davisonaudio/HapticInstrumentWorkshop/firmware/TeensyPlatformIO/include/ForceSensing.h

/*
 
ForceSensing.h
 
Author: Matt Davison
Date: 14/06/2024
 
*/

#pragma once

#include "au_GoertzelAlgorithm.h"
#include "au_Windowing.h"
#include "au_Onepole.h"

class ForceSensing
{
public:

    void setup();
    //Returns actual freq value (due to integer rounding)
    sample_t setResonantFrequencyHz(sample_t resonant_freq_hz);
    void setWindowSizePeriods(int window_size_periods);

    bool valueAvailable();

    void process(sample_t actuation_sample, sample_t sensed_sample);

    sample_t getDamping();
    int getWindowSizeSamples();
    int getWindowSizePeriods();

    /* 
     * This function should be called when the transducer is damped. it stores the last raw val as the calibration value
     * Note: make sure at least 1 window length has passed with the actuator damped before calling this function
     * Also ensure that there is a tone at the resonant frequency, at the required signal level, before calibrating.
     */
    void calibrateDamped();

    /* 
     * This function should be called when the transducer is undamped. it stores the last raw val as the calibration value
     * Note: make sure at least 1 window length has passed with the actuator undamped before calling this function
     * Also ensure that there is a tone at the resonant frequency, at the required signal level, before calibrating.
     */
    void calibrateUndamped();

    void setRawDampedValue(float raw_damped);
    void setRawUndampedValue(float raw_undamped);

    sample_t getRawDampedValue();
    sample_t getRawUndampedValue();

    void setRawDebugPrint(bool enable_print);

    virtual void endOfWindow(){}

    /*
     * Resets indexes of Goertzel & Windowing object, restarts them at beginning of the window.
     * It also resets the windowing object window sizes to be equal to the goertzel object window lengths (in case of freq/period length change)
     */
    void reset();

private:

    RealtimeGoertzel m_actuation_signal_goertzel;
    RealtimeGoertzel m_sensed_signal_goertzel;

    Windowing m_actuation_signal_window;
    Windowing m_sensing_signal_window;

    Onepole m_force_sense_averaging;

    /*
     * Returns a normalised floating point value of the damping where 1 = undamped, 0 = damped
     * Note: damped & undamped calibration methods must be called first, otherwise this function won't do anything useful
     */
    sample_t mapRawValue(sample_t raw_val);

    sample_t m_undamped_calibration_val;
    sample_t m_damped_calibration_val;

    sample_t m_last_raw_difference_val;
    sample_t m_last_mapped_filtered_val;

    bool m_debug_raw_print_enabled = false;
    bool m_new_val_flag = false;

};


/*
 * ForceSensing Implementation
 */
void ForceSensing::setup()
{
    GoertzelAlgorithm::SetupParameters setup_parameters;
    setup_parameters.sample_rate = AUDIO_SAMPLE_RATE_EXACT;
    setup_parameters.target_frequency = 440.0;
    setup_parameters.window_size_periods = 1;

    m_actuation_signal_goertzel.setup(setup_parameters);
    m_sensed_signal_goertzel.setup(setup_parameters);

    m_force_sense_averaging.setB1(-0.7);

    reset();
}

sample_t ForceSensing::setResonantFrequencyHz(sample_t resonant_freq_hz)
{
    sample_t actual_freq = m_actuation_signal_goertzel.setTargetFrequencyHz(resonant_freq_hz);
    m_sensed_signal_goertzel.setTargetFrequencyHz(resonant_freq_hz);

    reset();
    return actual_freq;
}

void ForceSensing::setWindowSizePeriods(int window_size_periods)
{
    m_actuation_signal_goertzel.setWindowSizePeriods(window_size_periods);
    m_sensed_signal_goertzel.setWindowSizePeriods(window_size_periods);

    reset();
}

bool ForceSensing::valueAvailable()
{
    bool flag_state = m_new_val_flag;
    m_new_val_flag = false; //reset flag
    return flag_state;
}

void ForceSensing::process(sample_t actuation_sample, sample_t sensed_sample)
{
    //Apply window to signals & feed into Goertzel
    m_actuation_signal_goertzel.processSample(m_actuation_signal_window.applyWindowToSample(actuation_sample));
    m_sensed_signal_goertzel.processSample(m_sensing_signal_window.applyWindowToSample(sensed_sample));
    if (m_actuation_signal_goertzel.checkNewValFlag())
    {
        m_last_raw_difference_val = m_actuation_signal_goertzel.getLastMagnitude() - m_sensed_signal_goertzel.getLastMagnitude();
        m_new_val_flag = true;
        m_last_mapped_filtered_val = m_force_sense_averaging.process(mapRawValue(m_last_raw_difference_val));
        if (m_debug_raw_print_enabled)
        {
            printf("Raw force sense vals: actuation: %f, sense: %f \r\n",m_actuation_signal_goertzel.getLastMagnitude(), m_sensed_signal_goertzel.getLastMagnitude());
        }

        // printf("Actuate: %f, Sense: %f, Diff: %f\r\n", m_actuation_signal_goertzel.getLastPhase(), m_sensed_signal_goertzel.getLastPhase(), m_actuation_signal_goertzel.getLastPhase() -  m_sensed_signal_goertzel.getLastPhase());
        //  printf("Actuate:\r\n");
    }
}

sample_t ForceSensing::getDamping()
{
    return m_last_mapped_filtered_val;
}

int ForceSensing::getWindowSizeSamples()
{
    return m_actuation_signal_goertzel.getWindowLengthSamples();
}

int ForceSensing::getWindowSizePeriods()
{
    return m_actuation_signal_goertzel.getWindowLengthPeriods();
}

void ForceSensing::calibrateUndamped()
{
    m_undamped_calibration_val = m_last_raw_difference_val;
    printf("New undamped calibration value: %f \r\n", m_undamped_calibration_val);
}

void ForceSensing::calibrateDamped()
{
    m_damped_calibration_val = m_last_raw_difference_val;
    printf("New damped calibration value: %f \r\n", m_damped_calibration_val);
}

sample_t ForceSensing::mapRawValue(sample_t raw_val)
{
    sample_t value_range = m_undamped_calibration_val - m_damped_calibration_val;
    sample_t mapped_val = (raw_val - m_damped_calibration_val) / value_range;
    if (mapped_val < 0.0)
    {
        mapped_val = 0.0;
    }
    if (mapped_val > 1.0)
    {
        mapped_val = 1.0;
    }
    return mapped_val;
}

void ForceSensing::reset()
{
    m_actuation_signal_goertzel.reset();
    m_sensed_signal_goertzel.reset();
    
    m_actuation_signal_window.resetIndex();
    m_sensing_signal_window.resetIndex();

    m_actuation_signal_window.setWindowSizeSamples(m_actuation_signal_goertzel.getWindowLengthSamples());
    m_sensing_signal_window.setWindowSizeSamples(m_sensed_signal_goertzel.getWindowLengthSamples());
}

void ForceSensing::setRawDampedValue(float raw_damped)
{
    m_damped_calibration_val = raw_damped;
}

void ForceSensing::setRawUndampedValue(float raw_undamped)
{
    m_undamped_calibration_val = raw_undamped;
}

sample_t ForceSensing::getRawDampedValue()
{
    return m_damped_calibration_val;
}

sample_t ForceSensing::getRawUndampedValue()
{
    return m_undamped_calibration_val;
}

void ForceSensing::setRawDebugPrint(bool enable_print)
{
    m_debug_raw_print_enabled = enable_print;
}
