davisonaudio/HapticInstrumentWorkshop/firmware/TeensyPlatformIO/include/TeensyEeprom.h

/*

TeensyEeprom.h

Author: Matt Davison
Date: 13/11/2024

For more info on the Teensy EEPROM see: https://www.pjrc.com/teensy/td_libs_EEPROM.html

*/

#pragma once

//Include the Arduino EEPROM library
#include "EEPROM.h"
#include "AudioRouting.h"
#include "au_Biquad.h"


class TeensyEeprom
{
    /*
     * REGISTER MAP:
     * Floats stored first, then bytes
     */
    
    public:

        enum class FloatParameters
        {
            RESONANT_FREQUENCY_HZ = 0,
            RESONANT_GAIN_DB,
            RESONANT_Q,
            TONE_LEVEL_DB,
            INDUCTANCE_FILTER_COEFFICIENT,
            BROADBAND_GAIN_DB,
            SAMPLE_RATE_HZ,
            UNDAMPED_CALIBRATION_VALUE,
            DAMPED_CALIBRATION_VALUE,
            OUTPUT_LPF_CUTOFF_HZ,
            INPUT_LPF_CUTOFF_HZ,
            HEADPHONE_LEVEL_DB,
            ACTUATION_LEVEL_DB,
            INDUCTANCE_BQ_A0,
            INDUCTANCE_BQ_A1,
            INDUCTANCE_BQ_A2,
            INDUCTANCE_BQ_B1,
            INDUCTANCE_BQ_B2,

            NUM_FLOAT_PARAMETERS
        };

        enum class ByteParameters
        {
            SERIAL_NUMBER = 0,
            BOARD_REVISION,
            LAST_SAVED_MAJ_VERSION,
            LAST_SAVED_MIN_VERSION,
            GOERTZEL_WINDOW_LENGTH,
            AUDIO_SHIELD_MODE,
            
            NUM_BYTE_PARAMETERS = 128 // Leave buffer to enable additional byte parameters while maintaining backwards compatibility
        };



        static const int NUM_EEPROM_BYTES = 1080; //Correct for Teensy 4.0
        static constexpr int BYTES_PER_FLOAT = sizeof(float);

        
        static constexpr int BYTES_BASE = 0;
        static constexpr int FLOATS_BASE = BYTES_BASE + static_cast<int>(ByteParameters::NUM_BYTE_PARAMETERS);

        void write(ByteParameters byte_parameter, uint8_t value)
        {
            EEPROM.write(getEepromAddress(byte_parameter), value);
        }
        uint8_t read(ByteParameters byte_parameter)
        {
            return EEPROM.read(getEepromAddress(byte_parameter));
        }

        void write(FloatParameters float_parameter, float value)
        {
            writeFloat(getEepromAddress(float_parameter), value);
        }

        float read(FloatParameters float_parameter)
        {
            return readFloat(getEepromAddress(float_parameter));
        }

        void writeBoardRevision(AudioRouting::BoardRevision board_revision)
        {
            write(ByteParameters::BOARD_REVISION, static_cast<uint8_t>(board_revision));
        }

        AudioRouting::BoardRevision readBoardRevision()
        {
            return static_cast<AudioRouting::BoardRevision>(read(ByteParameters::BOARD_REVISION));
        }

        void writeAudioShieldMode(AudioRouting::AudioShieldMode shield_mode)
        {
            write(ByteParameters::AUDIO_SHIELD_MODE, static_cast<uint8_t>(shield_mode));
        }

        AudioRouting::AudioShieldMode readAudioShieldMode()
        {
            return static_cast<AudioRouting::AudioShieldMode>(read(ByteParameters::AUDIO_SHIELD_MODE));
        }

        void writeInductanceBiquad(Biquad::Coefficients coefficients)
        {
            write(FloatParameters::INDUCTANCE_BQ_A0, coefficients.a0);
            write(FloatParameters::INDUCTANCE_BQ_A1, coefficients.a1);
            write(FloatParameters::INDUCTANCE_BQ_A2, coefficients.a2);
            write(FloatParameters::INDUCTANCE_BQ_B1, coefficients.b1);
            write(FloatParameters::INDUCTANCE_BQ_B2, coefficients.b2);
        }

        Biquad::Coefficients readInductanceBiquad()
        {
            Biquad::Coefficients coefficients;
            coefficients.a0 = read(FloatParameters::INDUCTANCE_BQ_A0);
            coefficients.a1 = read(FloatParameters::INDUCTANCE_BQ_A1);
            coefficients.a2 = read(FloatParameters::INDUCTANCE_BQ_A2);
            coefficients.b1 = read(FloatParameters::INDUCTANCE_BQ_B1);
            coefficients.b2 = read(FloatParameters::INDUCTANCE_BQ_B2);
            return coefficients;
        }


    private:

        //Union is used to convert between float and bytes (sorry)
        union FloatByteConverter
        {
            float float_val;
            uint8_t byte_vals[sizeof(float)];
        };

        /*
         *
         *
         */
        void writeFloat(unsigned int eeprom_address, float float_to_write)
        {
            FloatByteConverter float_to_byte;
            float_to_byte.float_val = float_to_write;

            for (unsigned int i = 0 ; i < sizeof(float) ; i++ )
            {
                EEPROM.write(eeprom_address + i, float_to_byte.byte_vals[i]);
            }
        }

        /*
         *
         *
         */
        float readFloat(unsigned int eeprom_address)
        {
            FloatByteConverter bytes_to_float;

            for (unsigned int i = 0 ; i < sizeof(float) ; i++ )
            {
                bytes_to_float.byte_vals[i] = EEPROM.read(eeprom_address + i);
            }

            return bytes_to_float.float_val;
        }

        unsigned int getEepromAddress(FloatParameters eeprom_parameter)
        {
            return FLOATS_BASE + (BYTES_PER_FLOAT * (static_cast<unsigned int>(eeprom_parameter)));
        }

        unsigned int getEepromAddress(ByteParameters eeprom_parameter)
        {
            return BYTES_BASE + static_cast<unsigned int>(eeprom_parameter);
        }

};
